kennySzhucheng/-EnvMonitor/EnvMonitor/Drivers/BH1750/bh1750.h

/**
 * @file    bh1750.h
 * @brief   BH1750 光照传感器驱�?(I2C)
 */

#ifndef BH1750_H
#define BH1750_H

#include "stm32f1xx_hal.h"

#define BH1750_ADDR     0x46        /* 8�?I2C 地址 (ADDR 引脚接地) */

void BH1750_Init(void);
uint8_t BH1750_ReadLight(float *lux);

#endif
