kennySzhucheng/-EnvMonitor/EnvMonitor/Drivers/DHT22/dht22.h

/**
 * @file    dht22.h
 * @brief   DHT22 温湿度传感器驱动 �?单总线 (1-Wire)
 */

#ifndef DHT22_H
#define DHT22_H

#include "stm32f1xx_hal.h"

#define DHT22_OK        0
#define DHT22_ERR_CHECK 1
#define DHT22_ERR_TIMEO 2

void DHT22_Init(void);
uint8_t DHT22_Read(float *temperature, float *humidity);

#endif
