kennySzhucheng/-EnvMonitor/EnvMonitor/Drivers/LED/led.h

/**
 * @file    led.h
 * @brief   LED 驱动 �?红黄绿三色指示灯
 */

#ifndef LED_H
#define LED_H

#include "stm32f1xx_hal.h"

typedef enum {
    LED_RED = 0,
    LED_YELLOW,
    LED_GREEN,
    LED_COUNT
} LED_Color_t;

void LED_Init(void);
void LED_On(LED_Color_t color);
void LED_Off(LED_Color_t color);
void LED_Toggle(LED_Color_t color);
void LED_AllOff(void);

#endif
